katiekr/Senior-Design-Solar-Maximum/Planning/effortmatrix.PNG

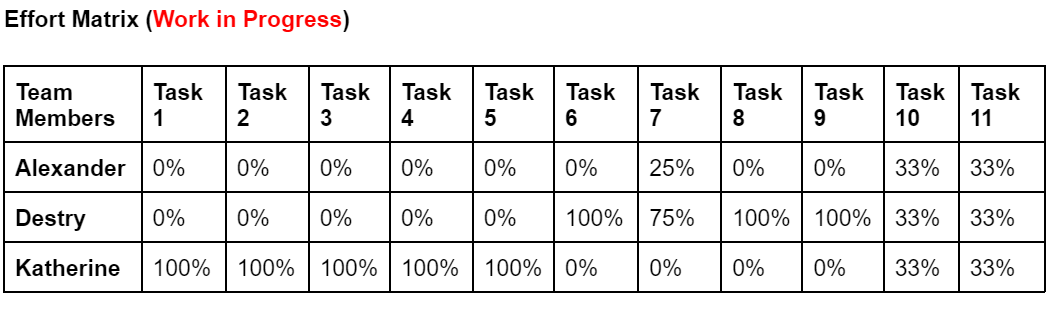
Planning/effortmatrix.PNG
