katiekr/Senior-Design-Solar-Maximum/3D Printer Files/Solar_Panel_Holder_Back.png

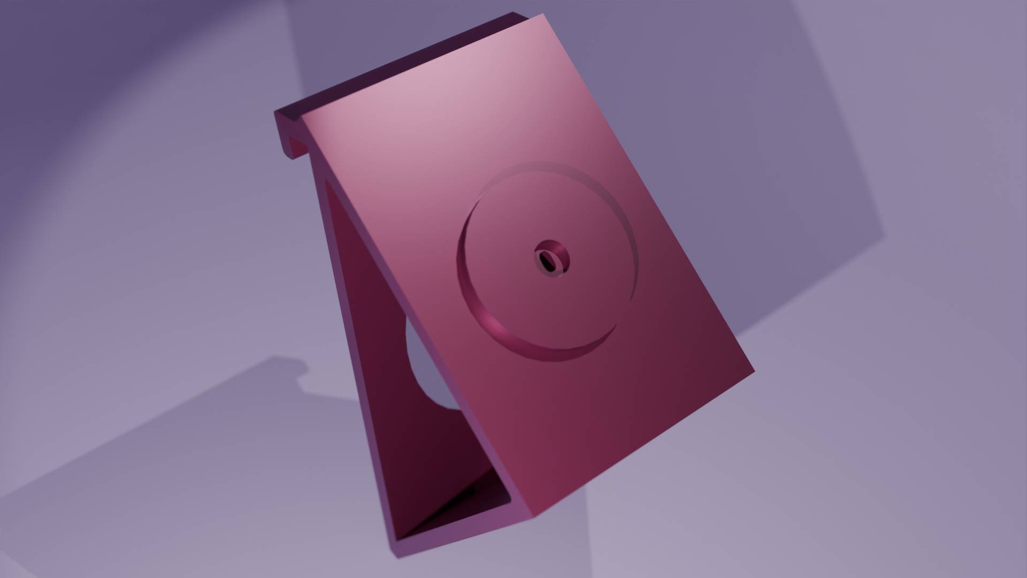
3D Printer Files/Solar_Panel_Holder_Back.png
