katiekr/Senior-Design-Solar-Maximum/3D Printer Files/Wire_Bottom.png

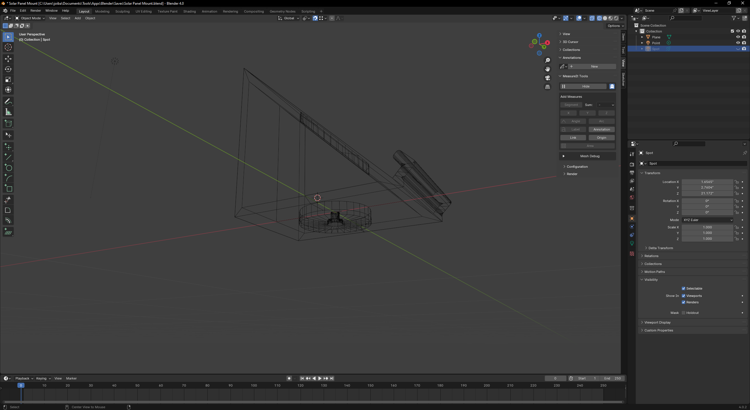
3D Printer Files/Wire_Bottom.png
