katiekr/Senior-Design-Solar-Maximum/3D Printer Files/Wire_Main.png

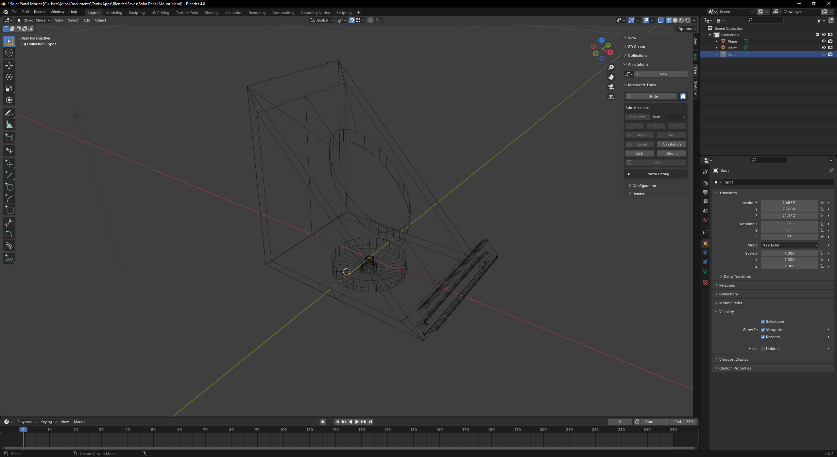
3D Printer Files/Wire_Main.png
