katiekr/Senior-Design-Solar-Maximum/Design/Circuits/Current_Testing.PNG

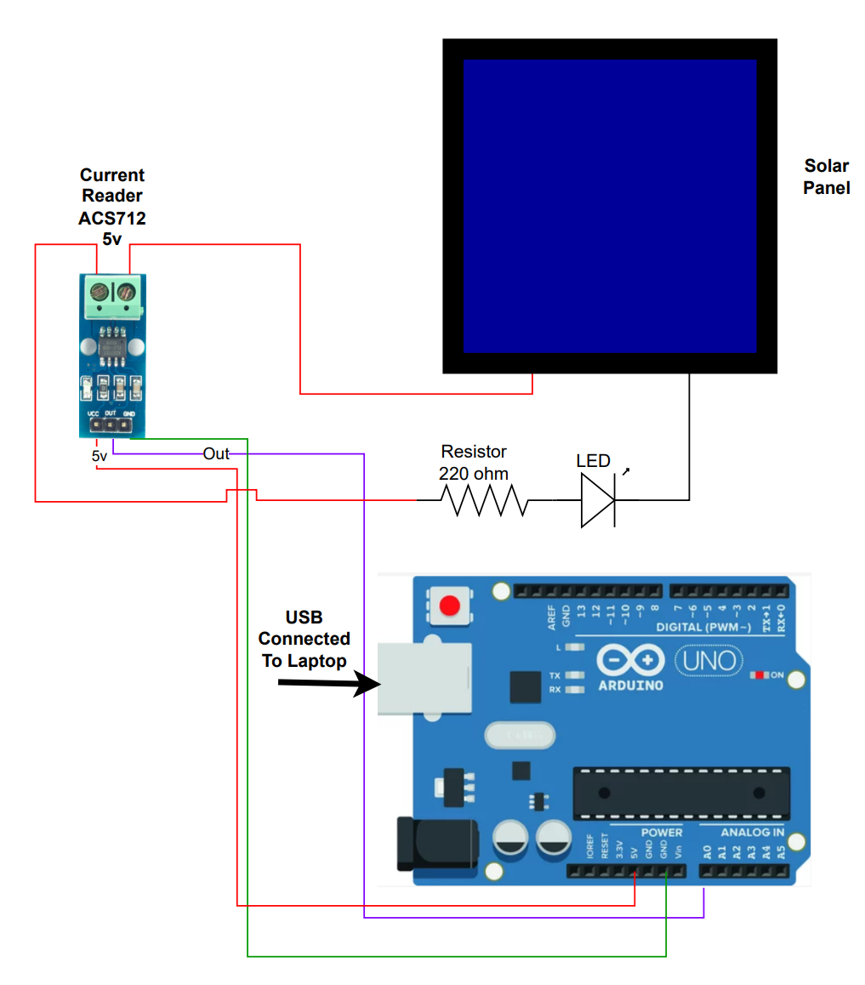
Design/Circuits/Current_Testing.PNG
